openCOVIDIndia/Sterilo_portable_sterilizer/doc/EN/img/IMG_6979-2.jpg

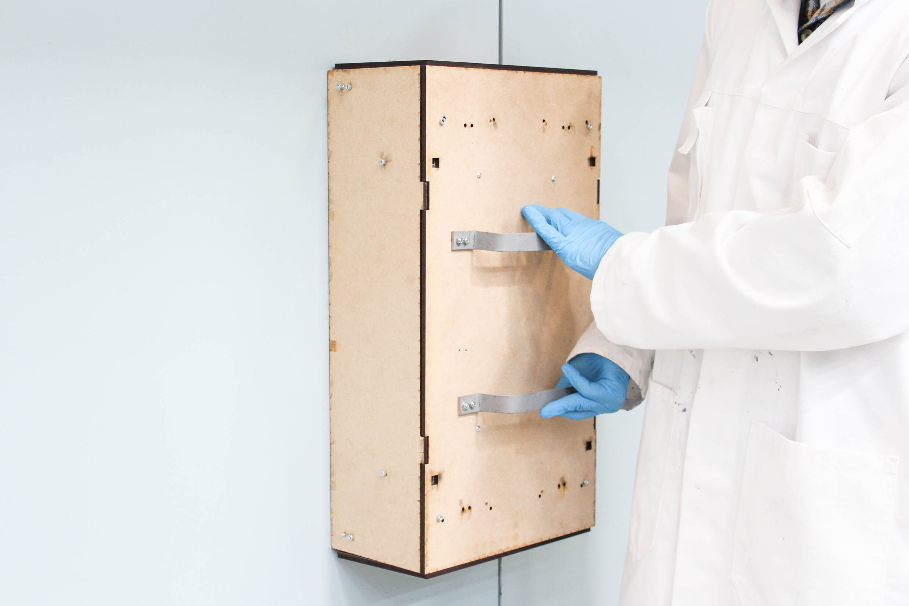
doc/EN/img/IMG_6979-2.jpg
