openCOVIDIndia/Sterilo_portable_sterilizer/doc/EN/img/research/Disinfection.jpg

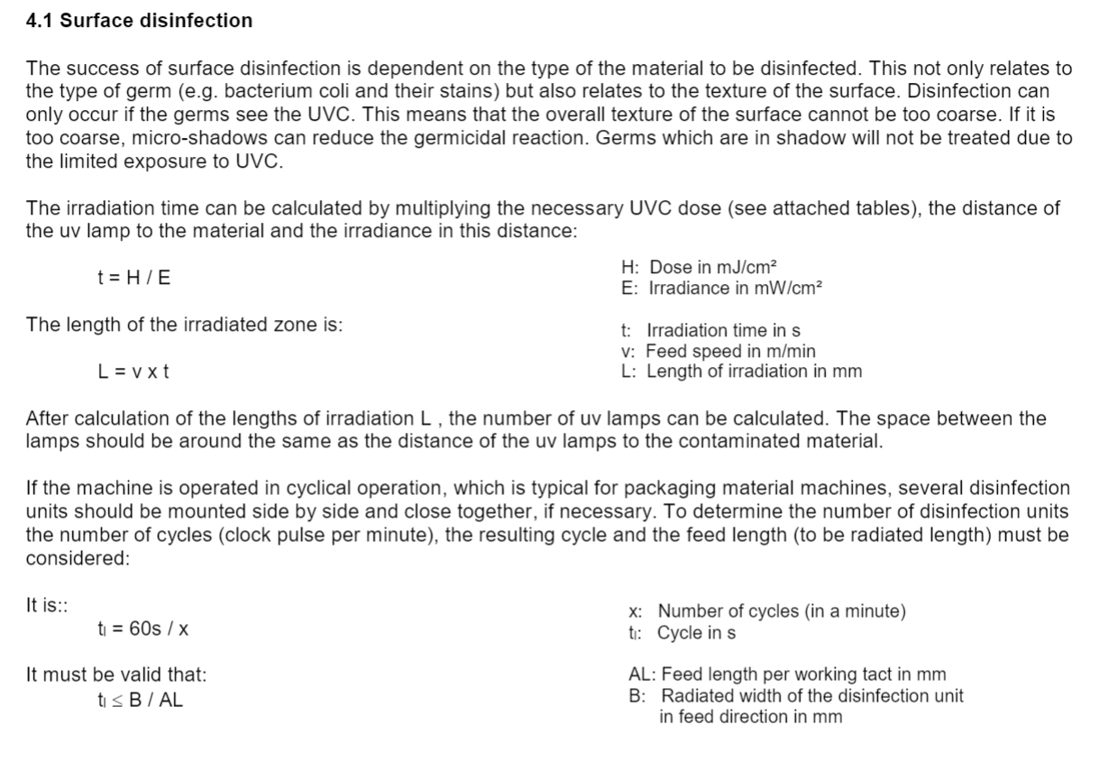
doc/EN/img/research/Disinfection.jpg
