openCOVIDIndia/Sterilo_portable_sterilizer/doc/EN/img/research/Humidity.jpg

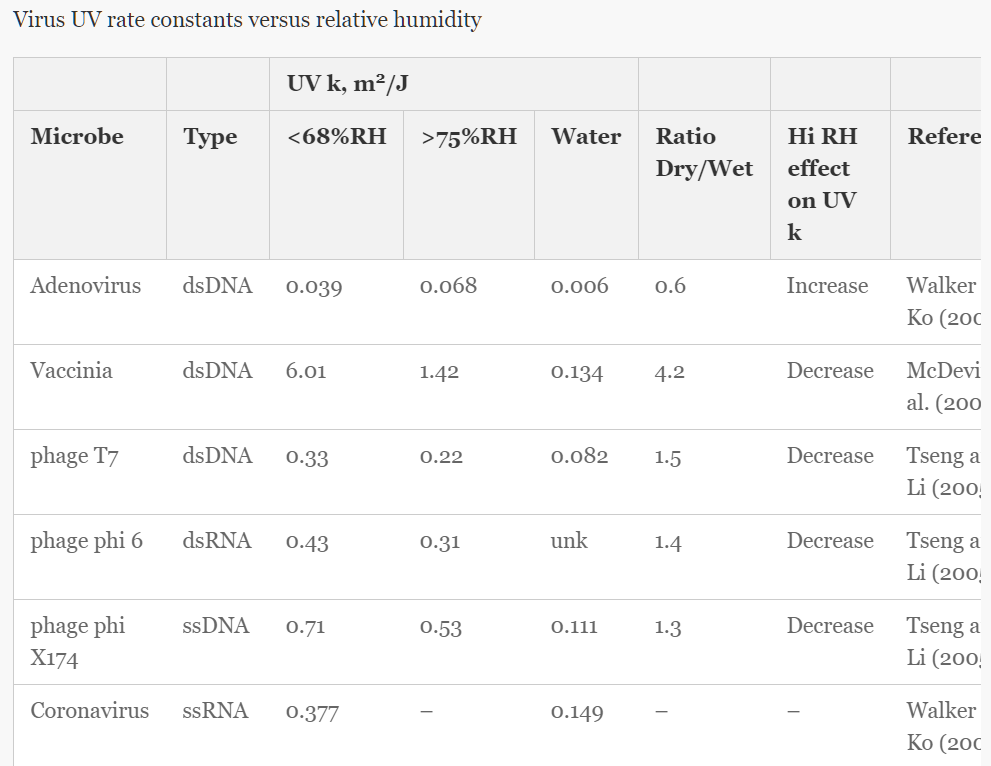
doc/EN/img/research/Humidity.jpg
