openCOVIDIndia/Sterilo_portable_sterilizer/doc/EN/img/research/inactivationdoses.jpg

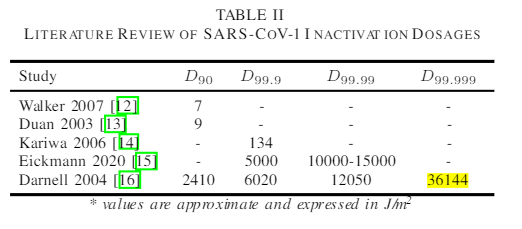
doc/EN/img/research/inactivationdoses.jpg
