openCOVIDIndia/Sterilo_portable_sterilizer/doc/EN/img/research/LEDvsLamps.png

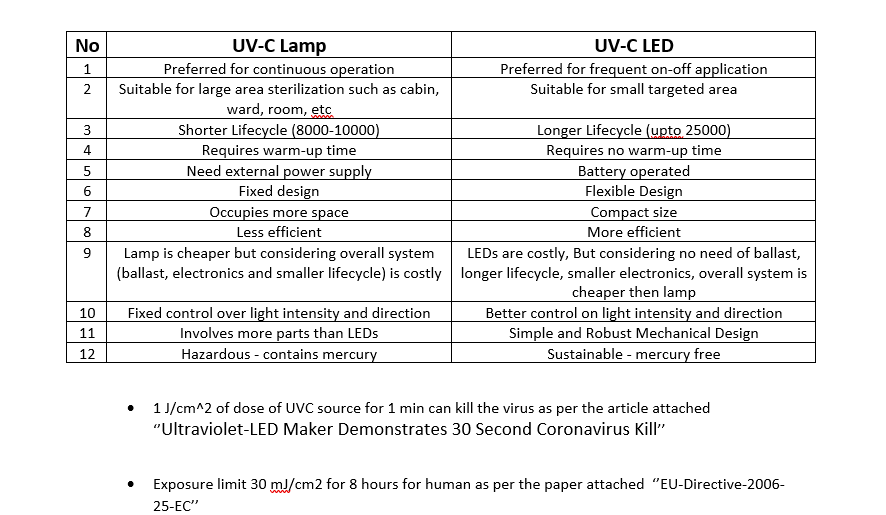
doc/EN/img/research/LEDvsLamps.png
