openCOVIDIndia/Sterilo_portable_sterilizer/doc/EN/img/research/temperature.jpg

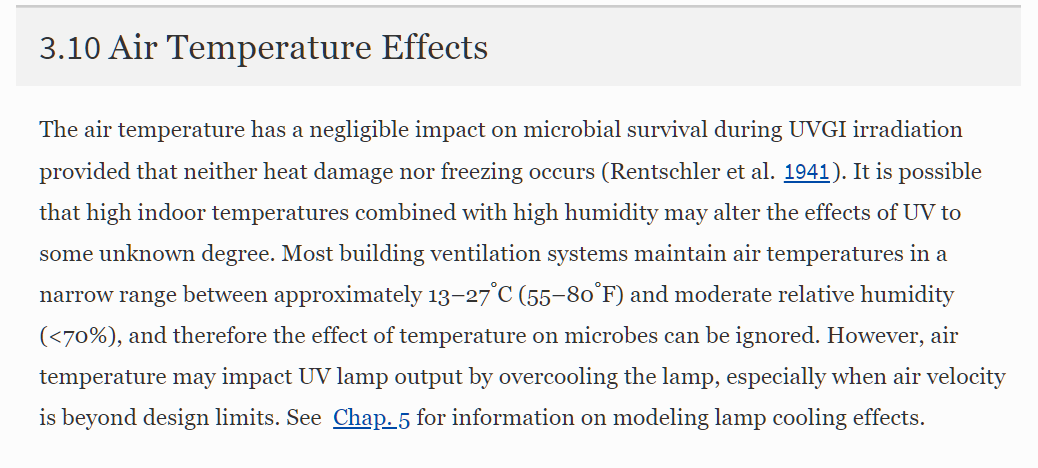
doc/EN/img/research/temperature.jpg
