openCOVIDIndia/Sterilo_portable_sterilizer/doc/EN/img/research/Time formula.jpg

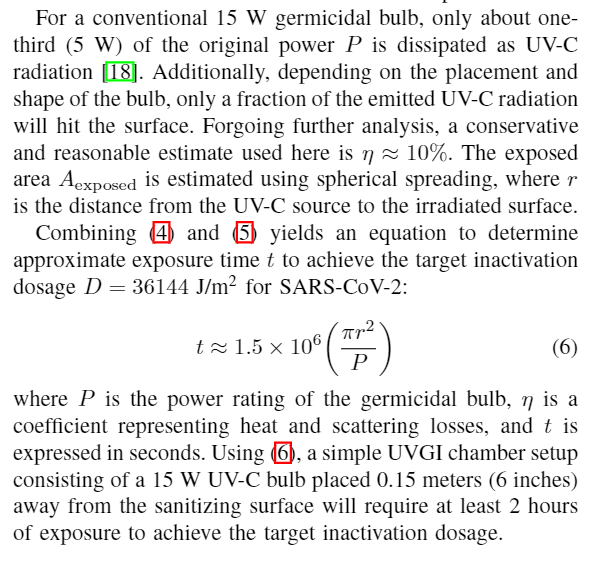
doc/EN/img/research/Time formula.jpg
