openCOVIDIndia/Sterilo_portable_sterilizer/doc/EN/img/research/UVefficiency.jpg

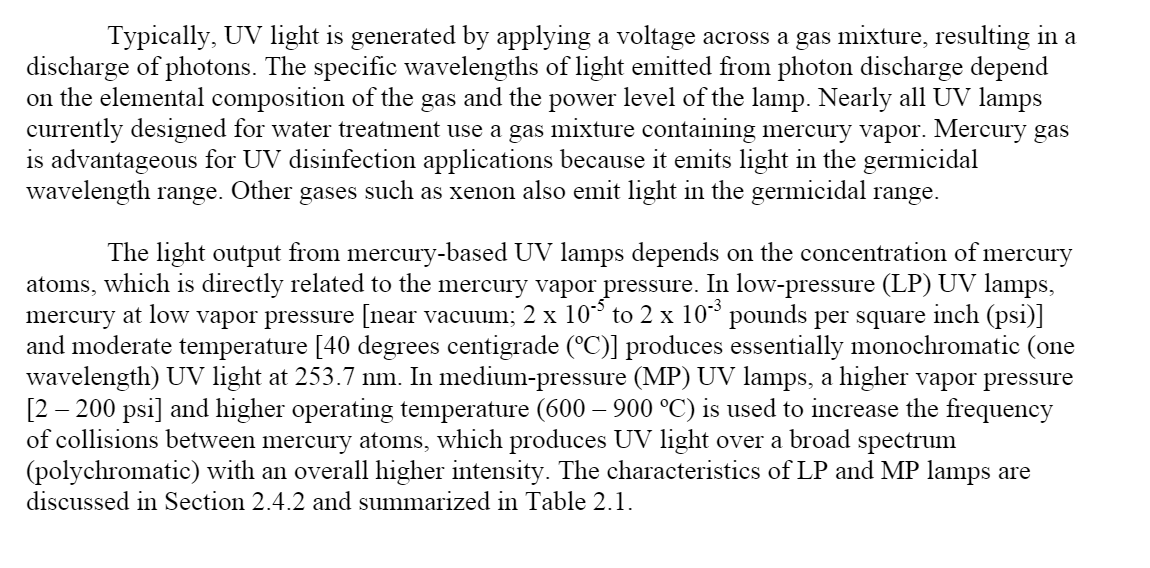
doc/EN/img/research/UVefficiency.jpg
