openCOVIDIndia/Sterilo_portable_sterilizer/doc/EN/img/research/UVGI.jpg

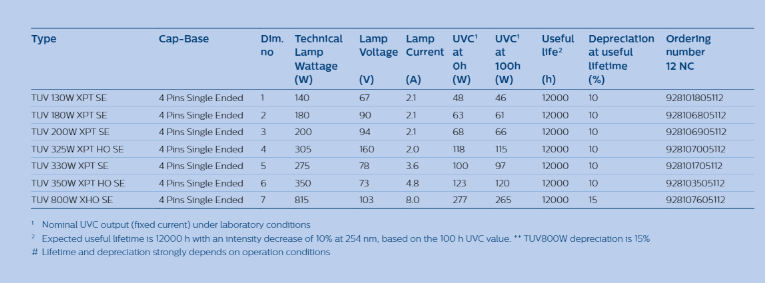
doc/EN/img/research/UVGI.jpg
