openCOVIDIndia/Sterilo_portable_sterilizer/doc/EN/img/research/UVmodels.jpg

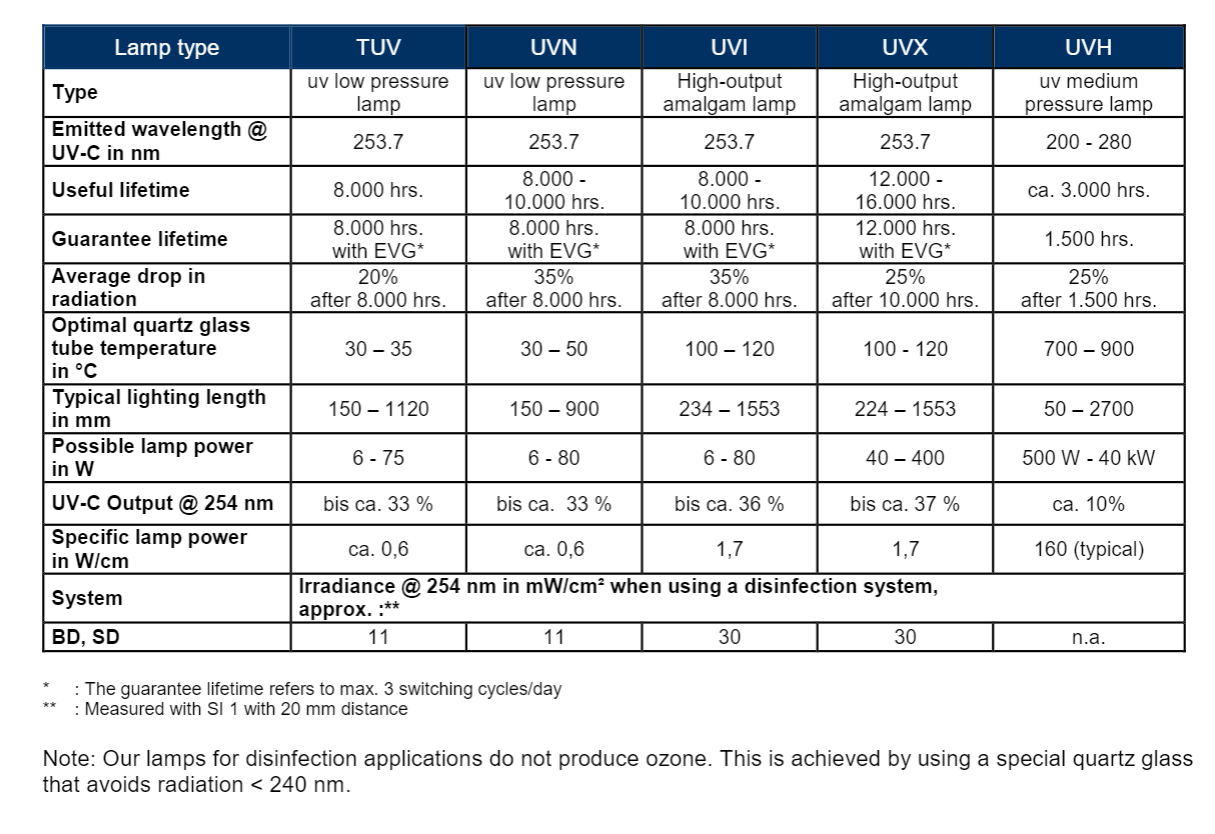
doc/EN/img/research/UVmodels.jpg
