openCOVIDIndia/Sterilo_portable_sterilizer/doc/EN/img/STERILO (9).png

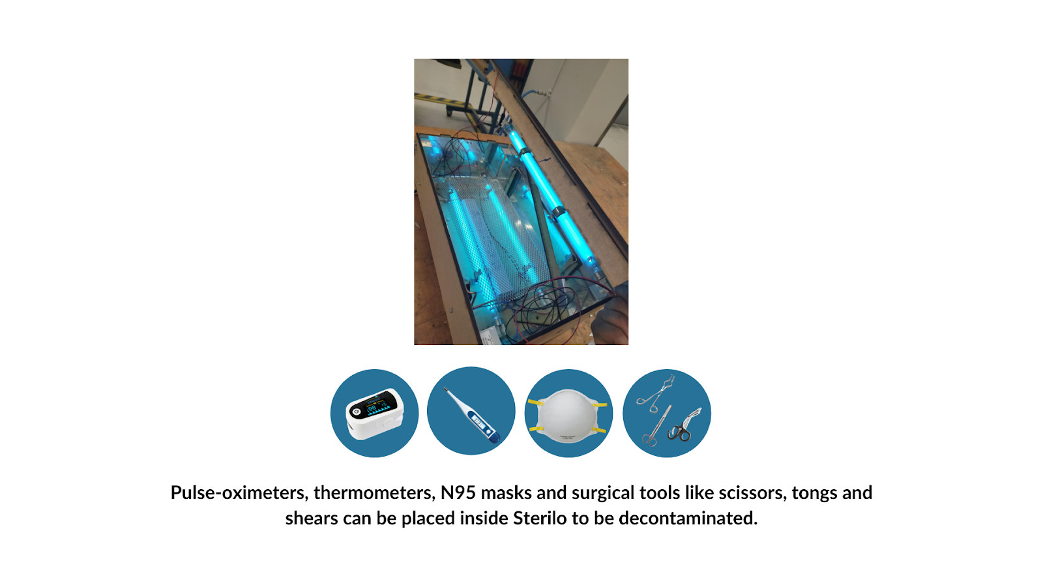
doc/EN/img/STERILO (9).png
