openCOVIDIndia/Sterilo_portable_sterilizer/doc/EN/img/V2 sterilo.PNG

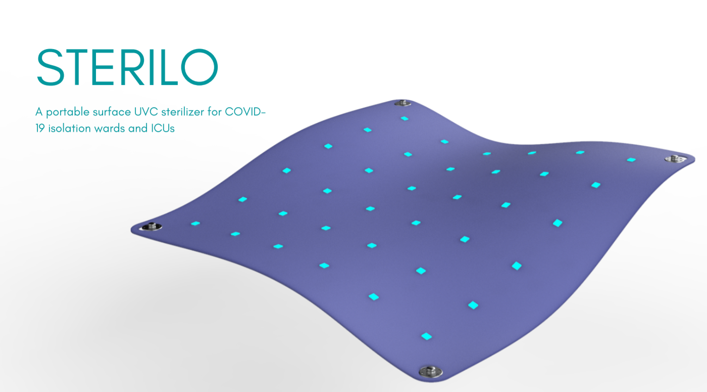
doc/EN/img/V2 sterilo.PNG
