openCOVIDIndia/Sterilo_portable_sterilizer/src/schematic/nano_schm.png

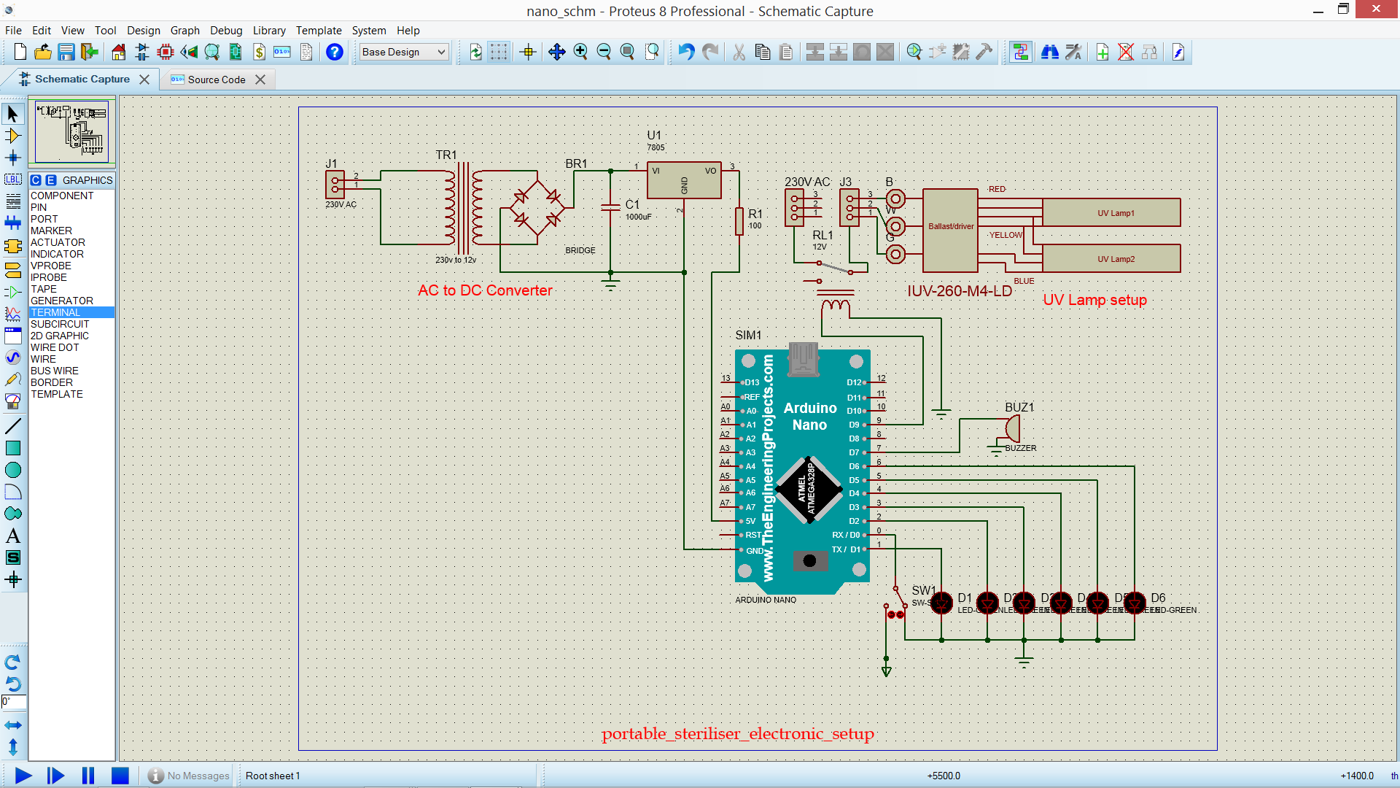
src/schematic/nano_schm.png
