openCOVIDIndia/Sterilo_portable_sterilizer/summary.jpg

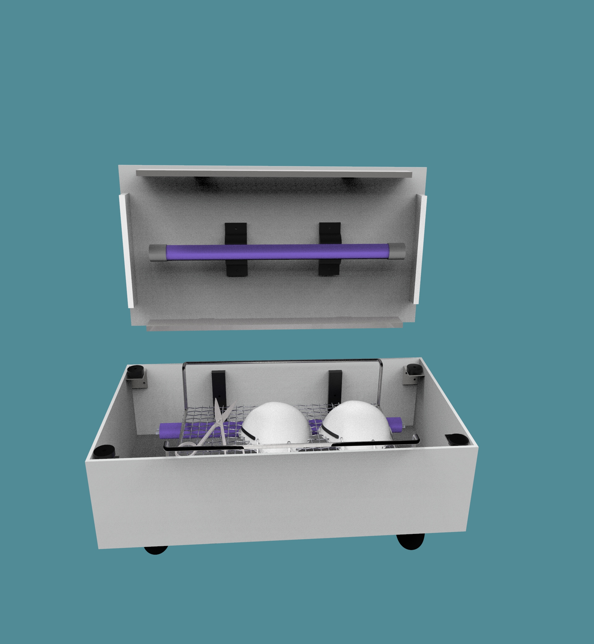
summary.jpg
