openCOVIDIndia/Sterilo_portable_sterilizer/src/PARTS/STEP Files/PC Sheet_shorter side_2.STEP

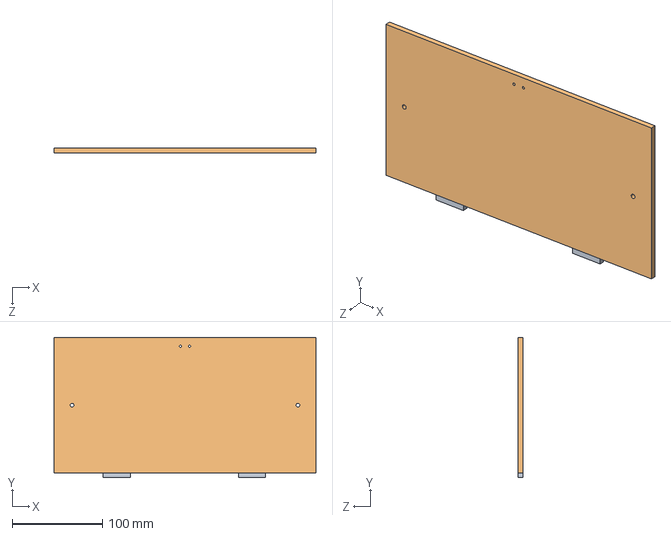
[picture p40: CAD file, 2020-04-13]
src/PARTS/STEP Files/PC Sheet_shorter side_2.STEP
290.0 x 155.1 x 5.00 mm
