openCOVIDIndia/Sterilo_portable_sterilizer/src/PARTS/STEP Files/Sheet Metal_Base.STEP

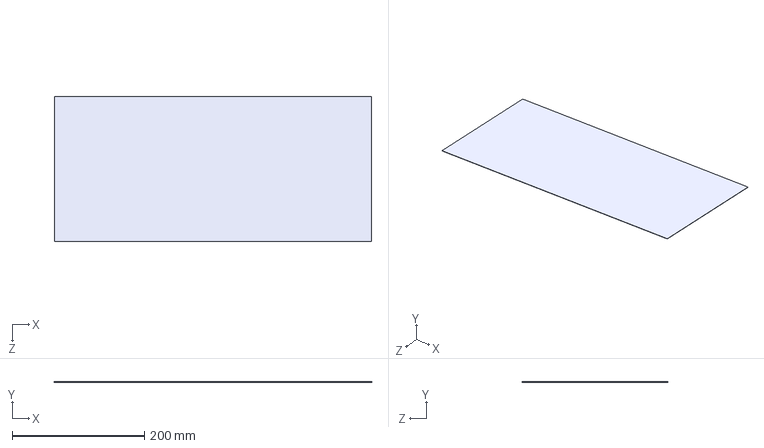
[picture p41: CAD file, 2020-04-13]
src/PARTS/STEP Files/Sheet Metal_Base.STEP
480.0 x 0.531 x 220.0 mm
