openCOVIDIndia/Sterilo_portable_sterilizer/src/PARTS/STEP Files/Grill Support_Short.STEP

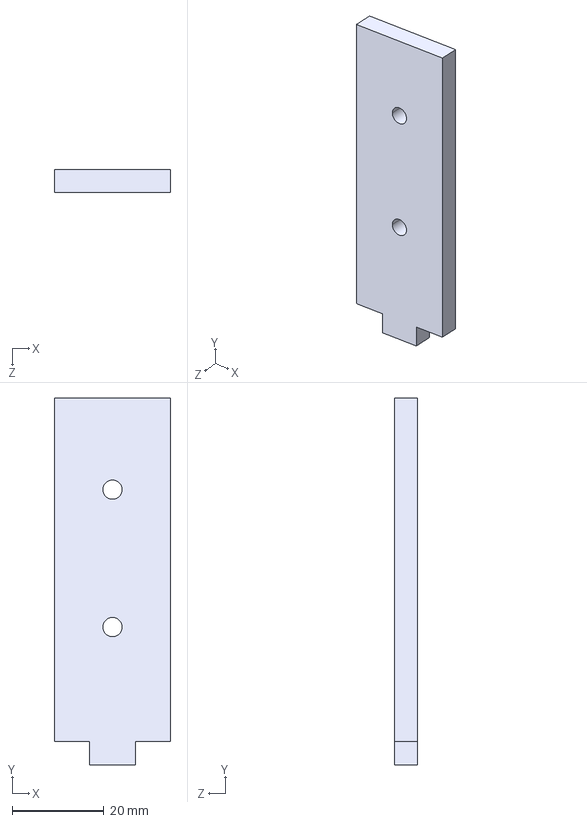
[picture p43: CAD file, 2020-04-13]
src/PARTS/STEP Files/Grill Support_Short.STEP
25.4 x 80.1 x 5.00 mm
