openCOVIDIndia/Sterilo_portable_sterilizer/src/PARTS/STEP Files/Electronics casing top.STEP

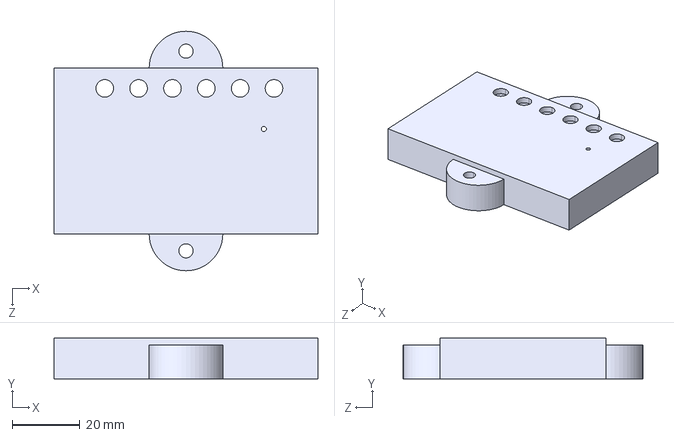
[picture p44: CAD file, 2020-04-13]
src/PARTS/STEP Files/Electronics casing top.STEP
78.0 x 12.0 x 70.8 mm
