openCOVIDIndia/Sterilo_portable_sterilizer/src/PARTS/STEP Files/Aluminium_Magnet holder.STEP

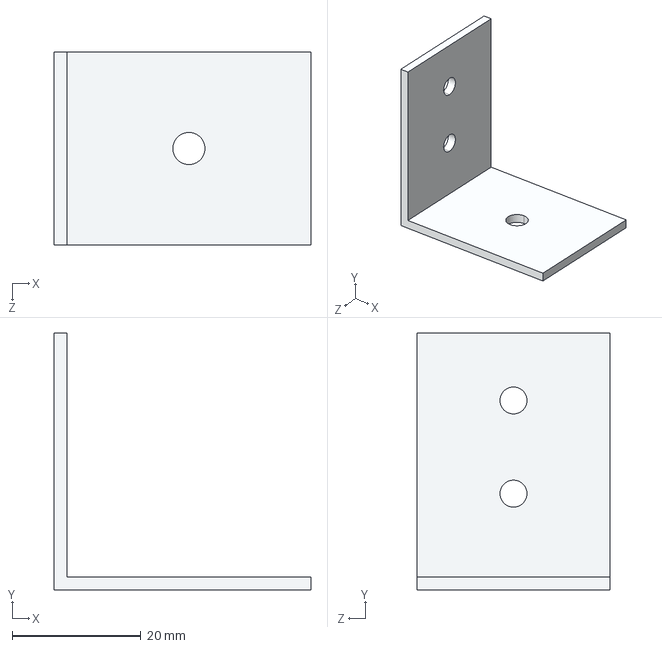
[picture p45: CAD file, 2020-04-13]
src/PARTS/STEP Files/Aluminium_Magnet holder.STEP
40.0 x 40.0 x 30.0 mm
