openCOVIDIndia/Sterilo_portable_sterilizer/src/PARTS/STEP Files/Metal handle.STEP

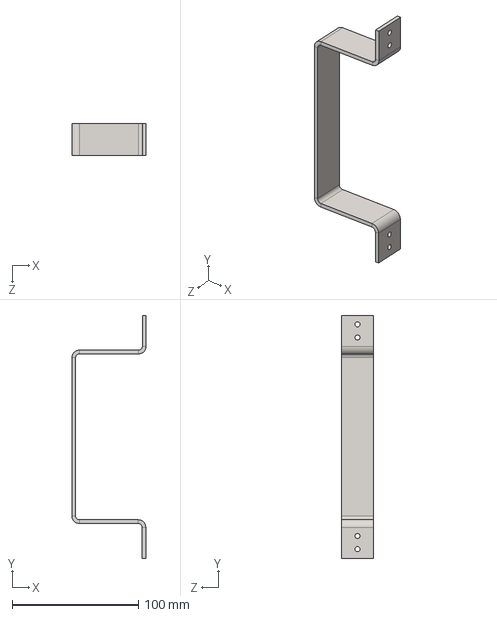
[picture p46: CAD file, 2020-04-13]
src/PARTS/STEP Files/Metal handle.STEP
58.8 x 192.3 x 25.4 mm
