openCOVIDIndia/Sterilo_portable_sterilizer/doc/EN/img/instructions/13.JPG

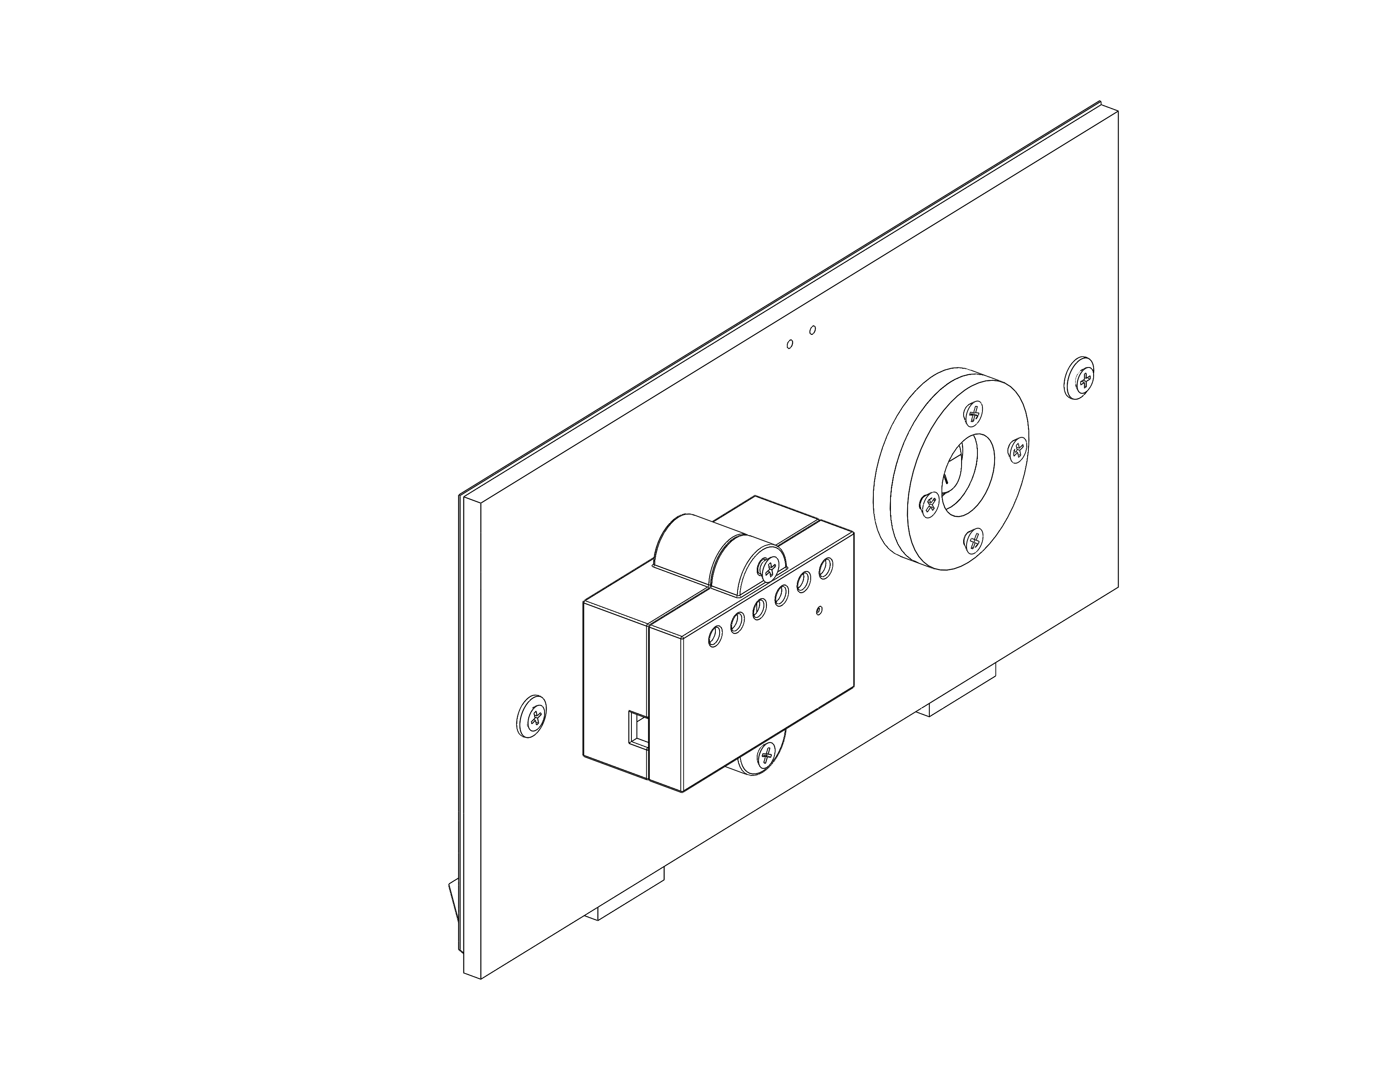
doc/EN/img/instructions/13.JPG
