openCOVIDIndia/Sterilo_portable_sterilizer/doc/EN/img/instructions/17.JPG

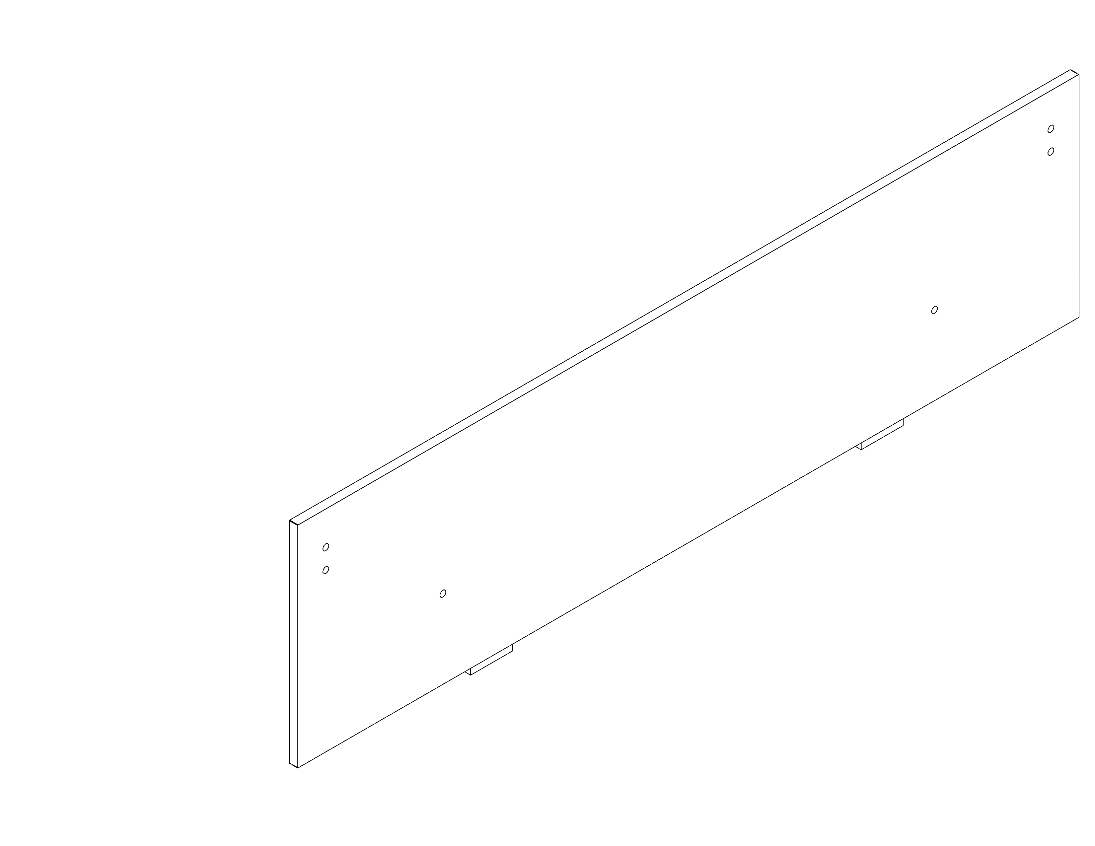
doc/EN/img/instructions/17.JPG
