openCOVIDIndia/Sterilo_portable_sterilizer/doc/EN/img/instructions/32.JPG

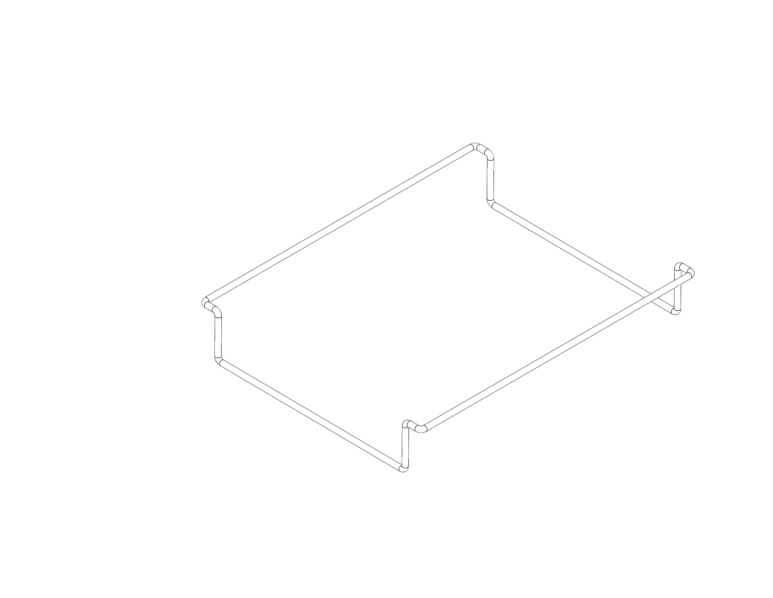
doc/EN/img/instructions/32.JPG
