openCOVIDIndia/Sterilo_portable_sterilizer/doc/EN/img/instructions/40.JPG

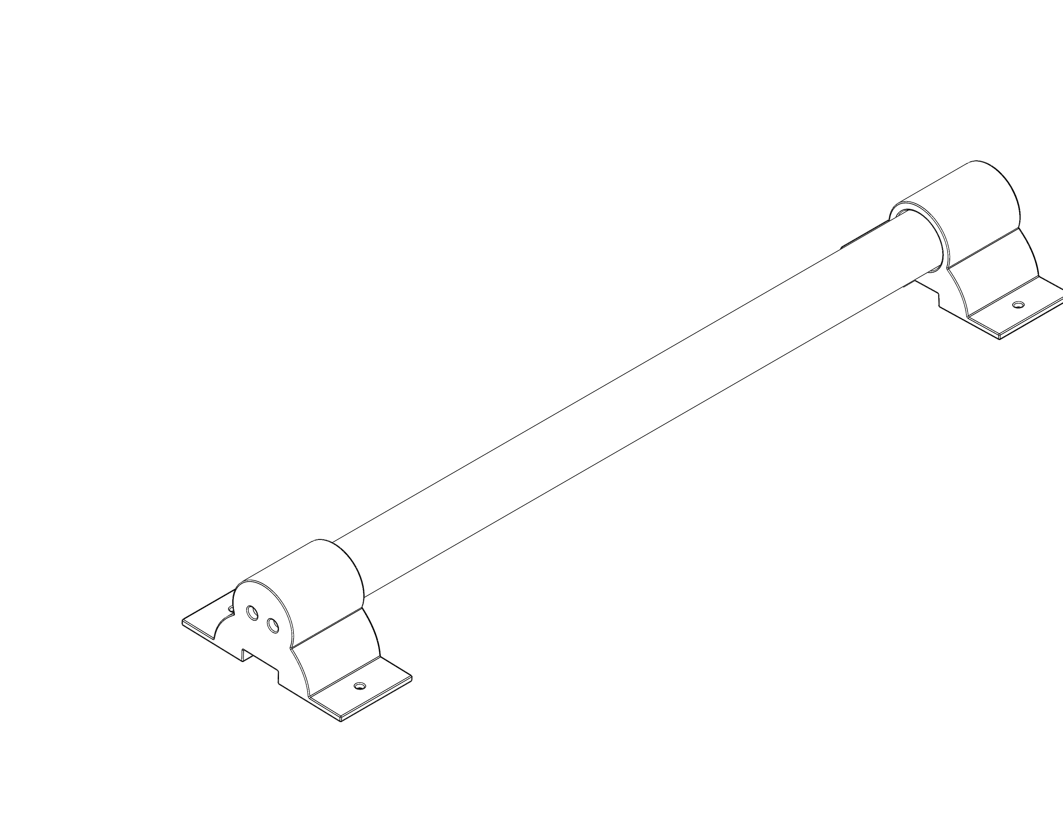
doc/EN/img/instructions/40.JPG
