openCOVIDIndia/Sterilo_portable_sterilizer/doc/EN/img/research/Measurement.png

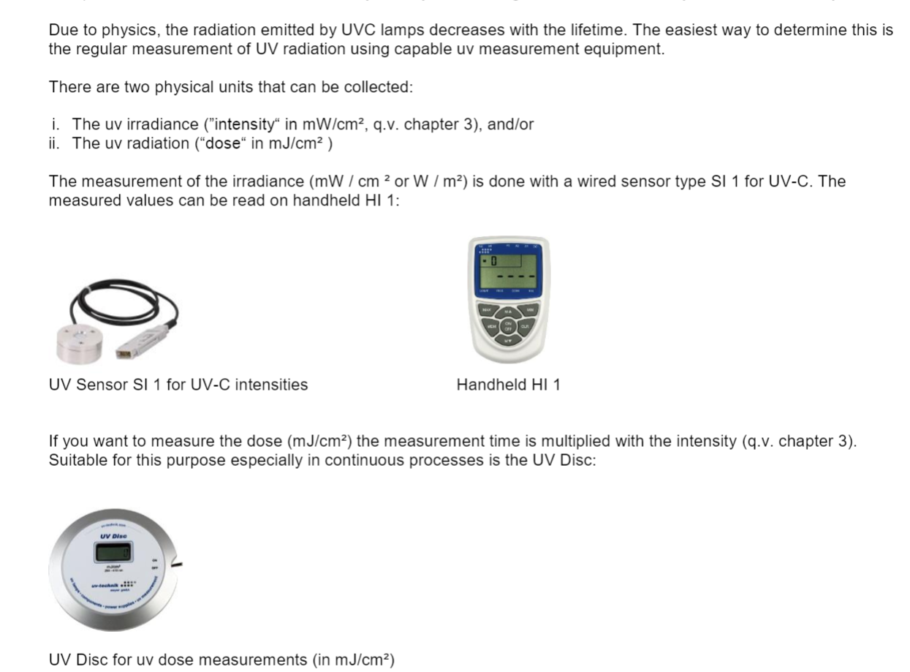
doc/EN/img/research/Measurement.png
